jenschr/Teensy3.2-example/images/heartbeat.jpg

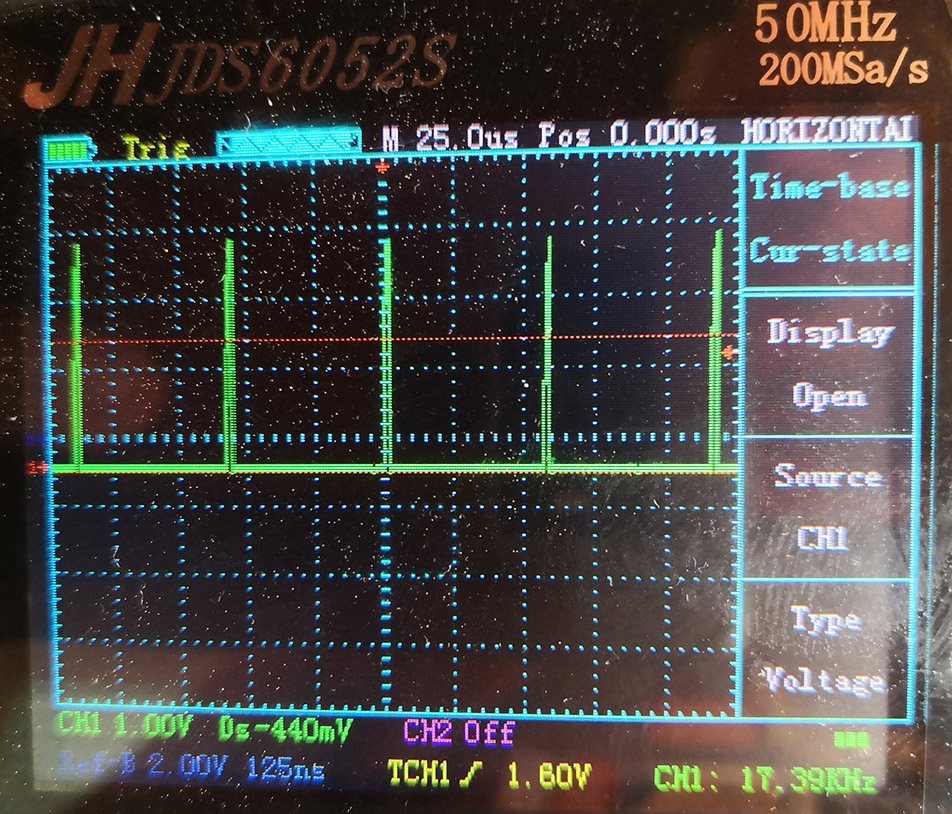
images/heartbeat.jpg
